TobleMiner/tiny-matrix/column.sch

## KiCad design column.sch (2020-10-23, an earlier design)

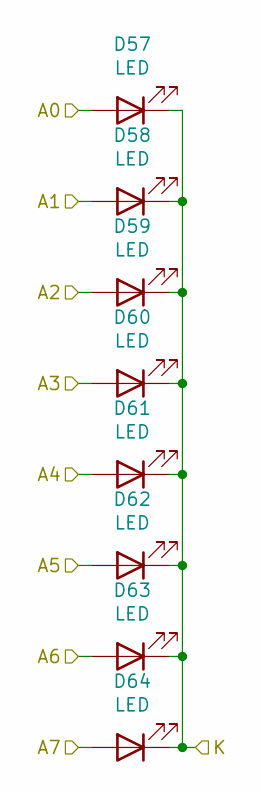
[picture p11: schematic column.sch]

Parts:
D1, D2, D3, D4, D5, D6, D7, D8: LED; LED_0402_1005Metric; LCSC C165980

Connections:
A0: D1.2 (A)
A1: D2.2 (A)
A2: D3.2 (A)
A3: D4.2 (A)
A4: D5.2 (A)
A5: D6.2 (A)
A6: D7.2 (A)
A7: D8.2 (A)
K: D1.1 (K), D2.1 (K), D3.1 (K), D4.1 (K), D5.1 (K), D6.1 (K), D7.1 (K), D8.1 (K)
