TobleMiner/tiny-matrix/tiny-led-matrix.sch

## KiCad design tiny-led-matrix.sch (2020-10-23, an earlier design)

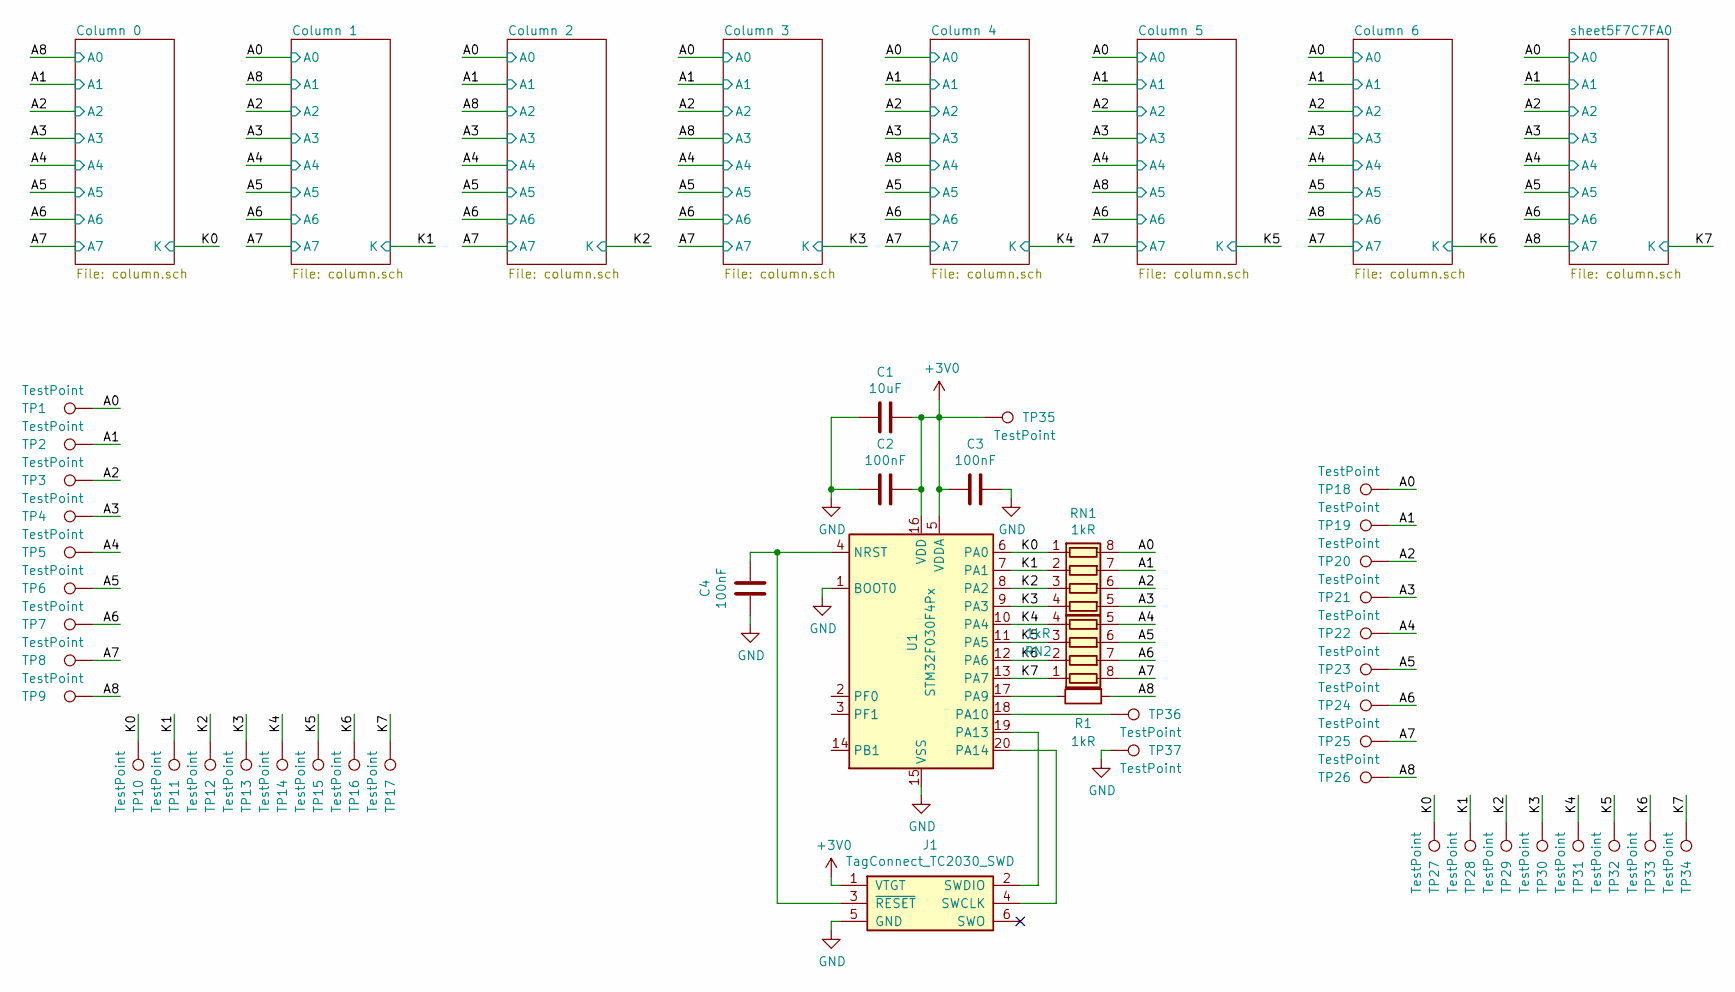
[picture p12: schematic tiny-led-matrix.sch]

Parts:
C1: 10uF; C_0402_1005Metric; LCSC C15525
C2, C3, C4: 100nF; C_0402_1005Metric; LCSC C1525
J1: TagConnect_TC2030_SWD; Tag-Connect_TC2030-IDC-NL_2x03_P1.27mm_Vertical
R1: 1kR; R_0402_1005Metric; LCSC C11702
RN1, RN2: 1kR; R_Array_Concave_4x0402; LCSC C25726
TP1, TP2, TP3, TP4, TP5, TP6, TP7, TP8, TP9, TP10, TP11, TP12, TP13, TP14, TP15, TP16, TP17, TP18, TP19, TP20, TP21, TP22, TP23, TP24, TP25, TP26, TP27, TP28, TP29, TP30, TP31, TP32, TP33, TP34, TP35, TP36, TP37: TestPoint; TestPoint_Pad_D1.0mm
U1: STM32F030F4Px; TSSOP-20_4.4x6.5mm_P0.65mm; LCSC C89040

Connections:
+3V0: C1.1, C2.1, C3.2, J1.1 (VTGT), TP35.1, U1.5 (VDDA), U1.16 (VDD)
A0: RN1.8 (R1.2), TP1.1, TP18.1
A1: RN1.7 (R2.2), TP2.1, TP19.1
A2: RN1.6 (R3.2), TP3.1, TP20.1
A3: RN1.5 (R4.2), TP4.1, TP21.1
A4: RN2.5 (R4.2), TP5.1, TP22.1
A5: RN2.6 (R3.2), TP6.1, TP23.1
A6: RN2.7 (R2.2), TP7.1, TP24.1
A7: RN2.8 (R1.2), TP8.1, TP25.1
A8: R1.2, TP9.1, TP26.1
GND: C1.2, C2.2, C3.1, C4.2, J1.5 (GND), TP37.1, U1.1 (BOOT0), U1.15 (VSS)
K0: RN1.1 (R1.1), TP10.1, TP27.1, U1.6 (PA0)
K1: RN1.2 (R2.1), TP11.1, TP28.1, U1.7 (PA1)
K2: RN1.3 (R3.1), TP12.1, TP29.1, U1.8 (PA2)
K3: RN1.4 (R4.1), TP13.1, TP30.1, U1.9 (PA3)
K4: RN2.4 (R4.1), TP14.1, TP31.1, U1.10 (PA4)
K5: RN2.3 (R3.1), TP15.1, TP32.1, U1.11 (PA5)
K6: RN2.2 (R2.1), TP16.1, TP33.1, U1.12 (PA6)
K7: RN2.1 (R1.1), TP17.1, TP34.1, U1.13 (PA7)
unnamed: C4.1, J1.3 (~RESET), U1.4 (NRST)
unnamed: J1.2 (SWDIO), U1.19 (PA13)
unnamed: J1.4 (SWCLK), U1.20 (PA14)
unnamed: R1.1, U1.17 (PA9)
unnamed: TP36.1, U1.18 (PA10)
